SolderedElectronics/Dasduino-CONNECTPLUS-hardware-design/OUTPUTS/V1.1.1/333033 (2).jpg

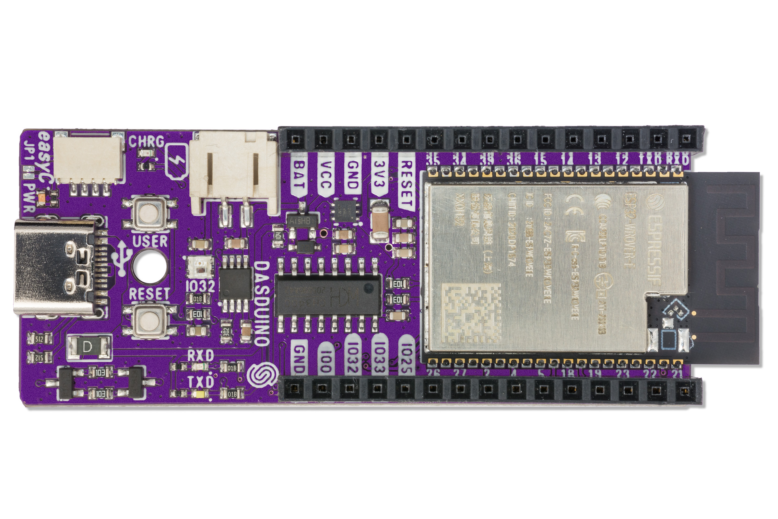
OUTPUTS/V1.1.1/333033 (2).jpg
