SolderedElectronics/Dasduino-CONNECTPLUS-hardware-design/OUTPUTS/V1.1.1/333033.jpg

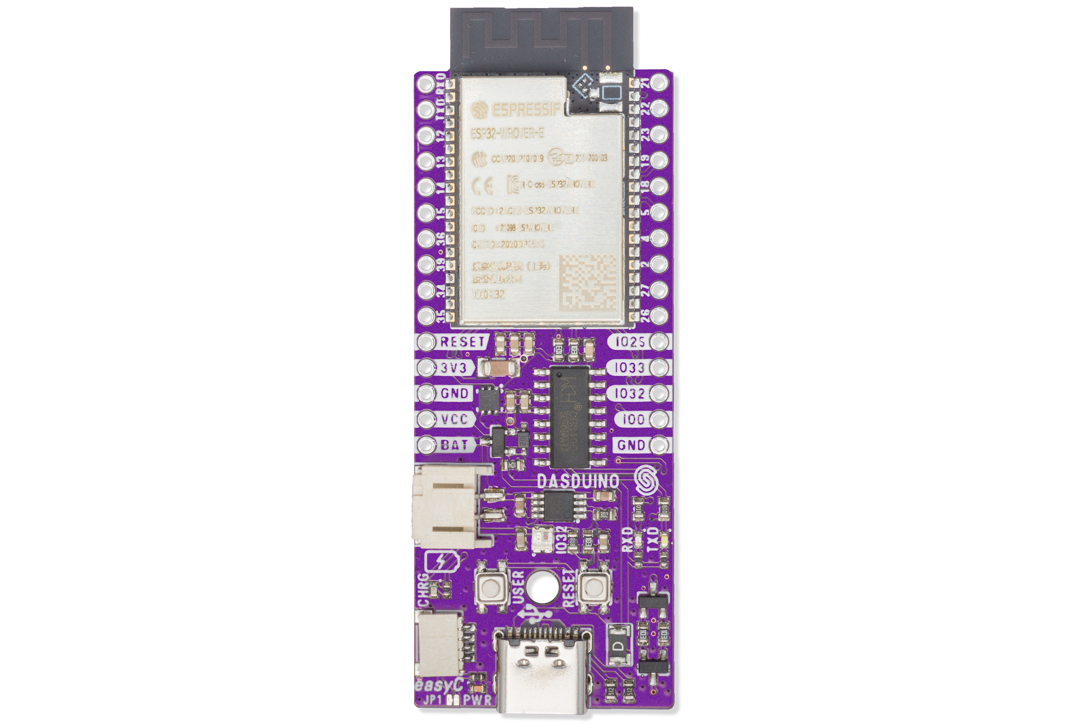
OUTPUTS/V1.1.1/333033.jpg
