SolderedElectronics/Dasduino-CONNECTPLUS-hardware-design/OUTPUTS/V1.1.1/Dasduino CONNECTPLUS Pinout.jpg

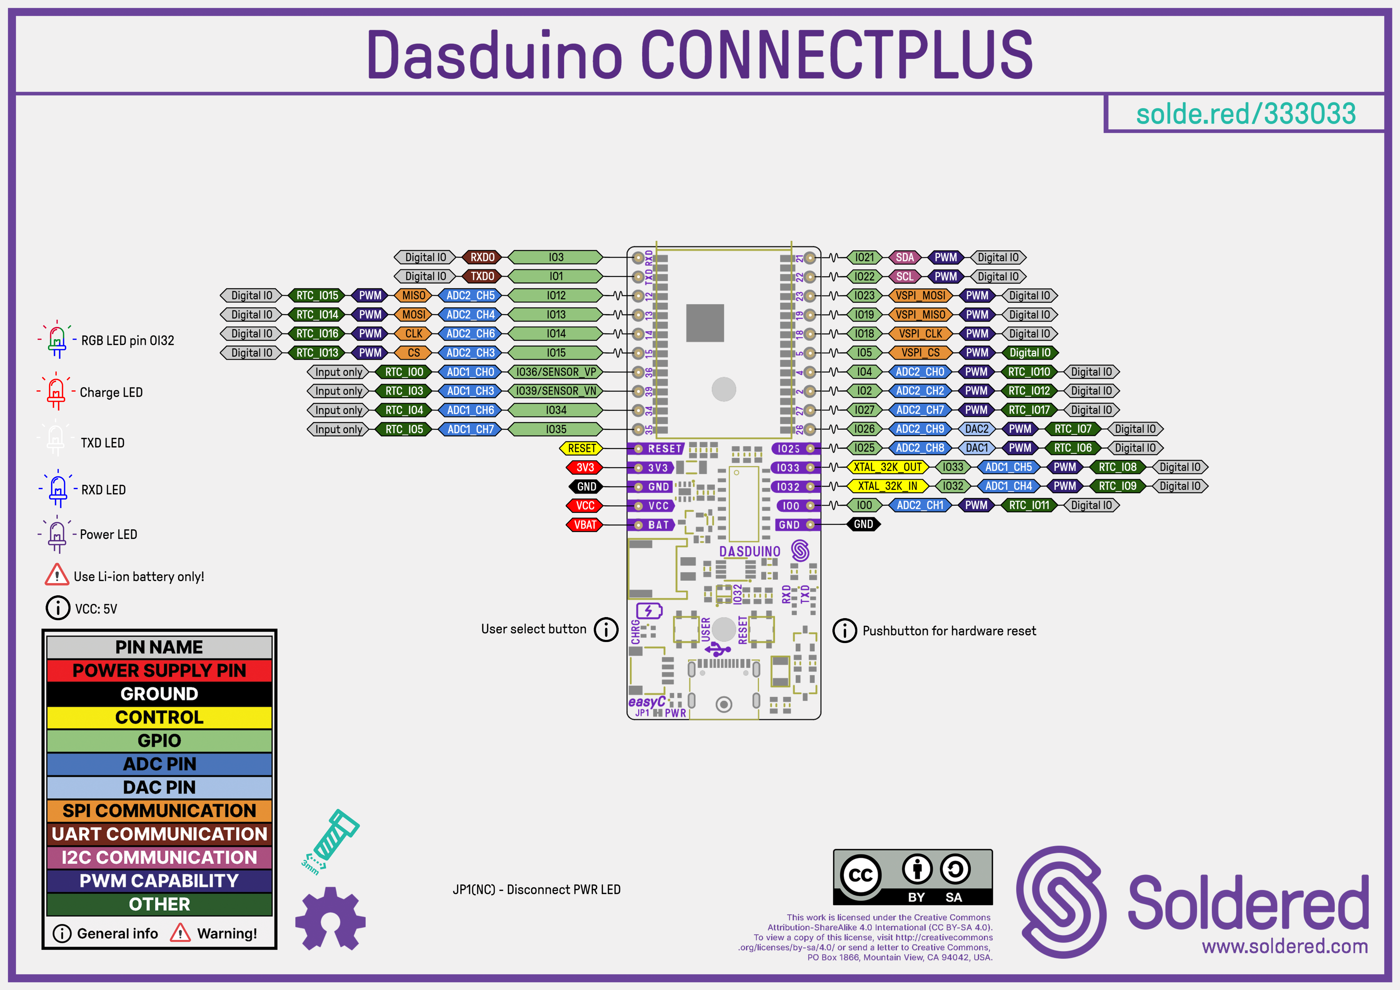
OUTPUTS/V1.1.1/Dasduino CONNECTPLUS Pinout.jpg
